Oz-113/deskie-vibed/source_frames/lucycigarette_7.png

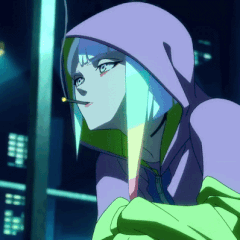
source_frames/lucycigarette_7.png
