Oz-113/deskie-vibed/source_frames/2b_0.png

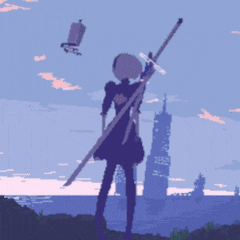
source_frames/2b_0.png
