Oz-113/deskie-vibed/source_frames/cirilla_0.png

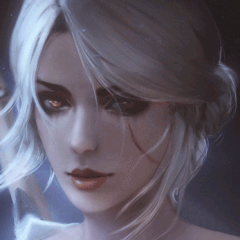
source_frames/cirilla_0.png
