Oz-113/deskie-vibed/source_frames/cirilla_11.png

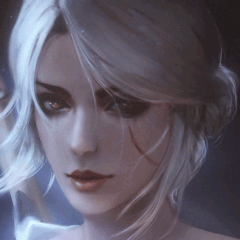
source_frames/cirilla_11.png
