Oz-113/deskie-vibed/source_frames/lucybg_0.png

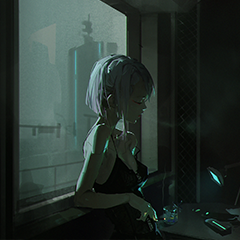
source_frames/lucybg_0.png
