Oz-113/deskie-vibed/source_frames/lucydavidmoon_0.png

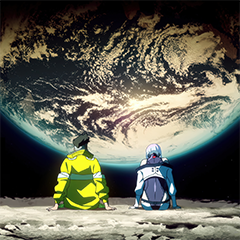
source_frames/lucydavidmoon_0.png
