Oz-113/deskie-vibed/CAD/hazir parcalar/esp32-s3-wroom-1-1.snapshot.2/WS2812B.SLDPRT

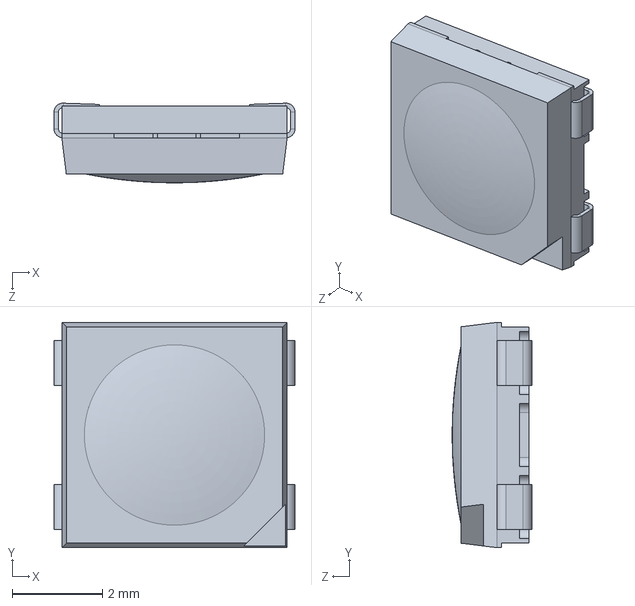
[picture p19: CAD file, 2026-09-12]
CAD/hazir parcalar/esp32-s3-wroom-1-1.snapshot.2/WS2812B.SLDPRT
5.35 x 5.00 x 1.77 mm
