Oz-113/deskie-vibed/CAD/hazir parcalar/esp32-s3-wroom-1-1.snapshot.2/SOT23-3.SLDPRT

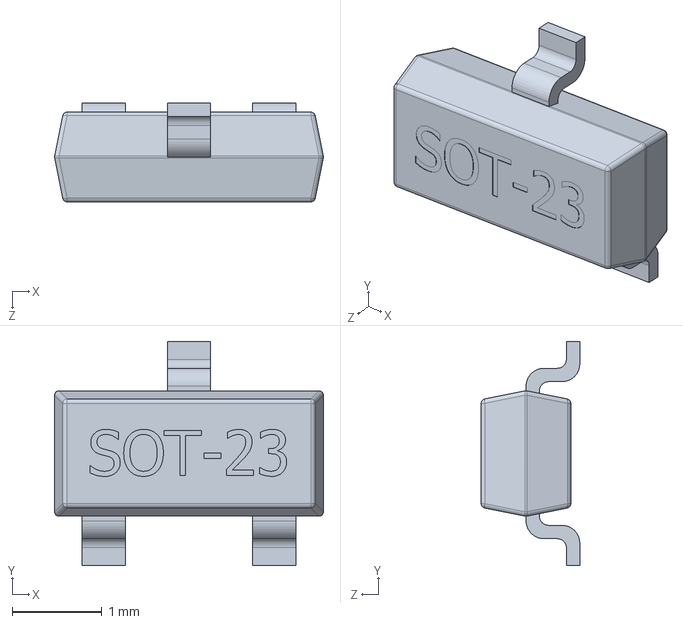
[picture p20: CAD file, 2026-09-12]
CAD/hazir parcalar/esp32-s3-wroom-1-1.snapshot.2/SOT23-3.SLDPRT
3.00 x 2.50 x 1.10 mm
