Oz-113/deskie-vibed/CAD/hazir parcalar/esp32-s3-wroom-1-1.snapshot.2/SOD-123F.SLDPRT

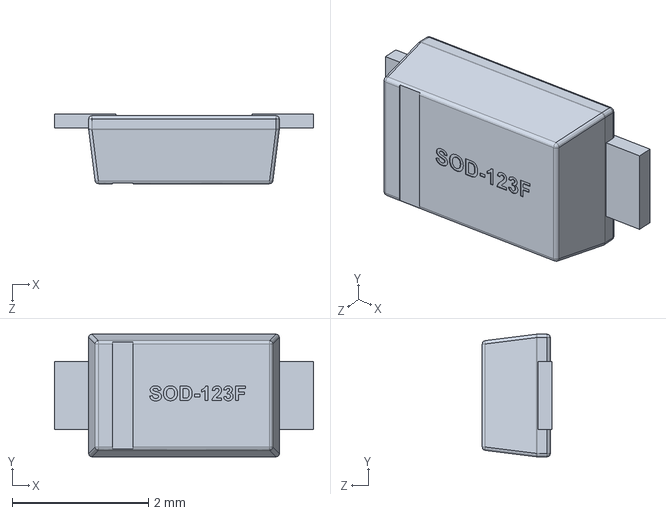
[picture p21: CAD file, 2026-09-12]
CAD/hazir parcalar/esp32-s3-wroom-1-1.snapshot.2/SOD-123F.SLDPRT
3.80 x 1.80 x 1.02 mm
