Oz-113/deskie-vibed/CAD/hazir parcalar/esp32-s3-wroom-1-1.snapshot.2/ctantal_case-a_l3-2_w1-6_h1-6.SLDPRT

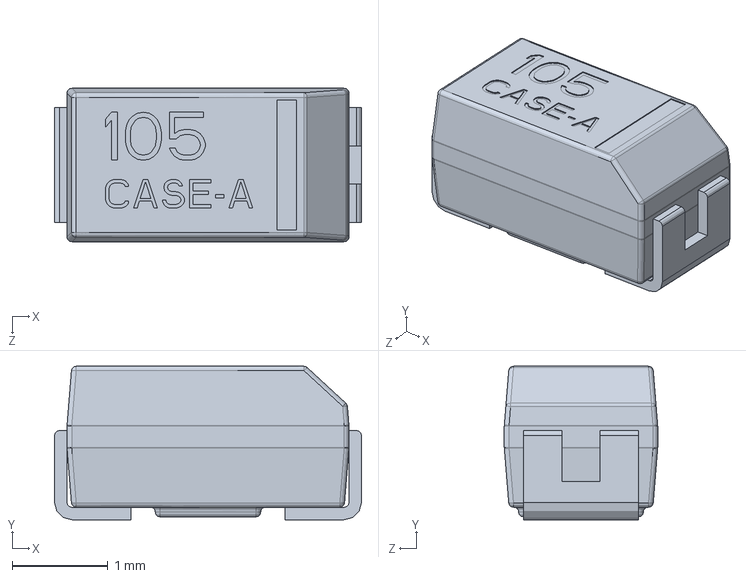
[picture p22: CAD file, 2026-09-12]
CAD/hazir parcalar/esp32-s3-wroom-1-1.snapshot.2/ctantal_case-a_l3-2_w1-6_h1-6.SLDPRT
3.20 x 1.60 x 1.60 mm
