Oz-113/deskie-vibed/CAD/hazir parcalar/esp32-s3-wroom-1-1.snapshot.2/RC0402.SLDPRT

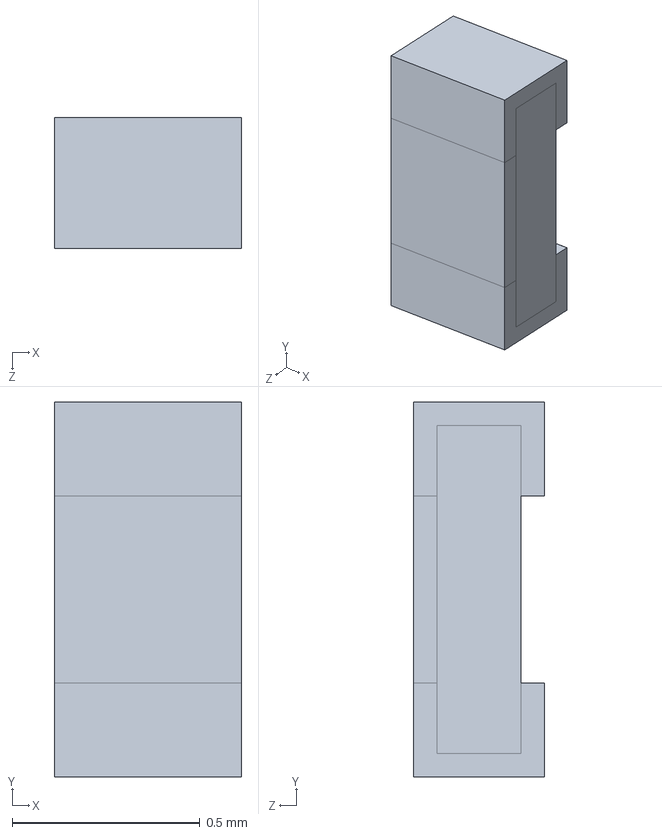
[picture p23: CAD file, 2026-09-12]
CAD/hazir parcalar/esp32-s3-wroom-1-1.snapshot.2/RC0402.SLDPRT
0.5 x 1.00 x 0.35 mm
