Oz-113/deskie-vibed/CAD/hazir parcalar/esp32-s3-wroom-1-1.snapshot.2/QFN-16 (3x3).SLDASM

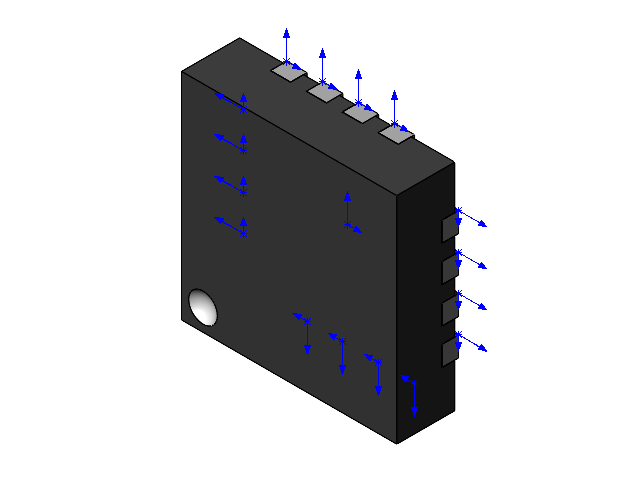
[picture p26: CAD file, 2026-09-12]
CAD/hazir parcalar/esp32-s3-wroom-1-1.snapshot.2/QFN-16 (3x3).SLDASM
QFN-16 (3x3) Part1.stp
QFN-16 (3x3) Part2.stp x 16
eBom-FreeParts.stp
