Oz-113/deskie-vibed/CAD/hazir parcalar/esp32-s3-wroom-1-1.snapshot.2/LED_0603 v4.SLDASM

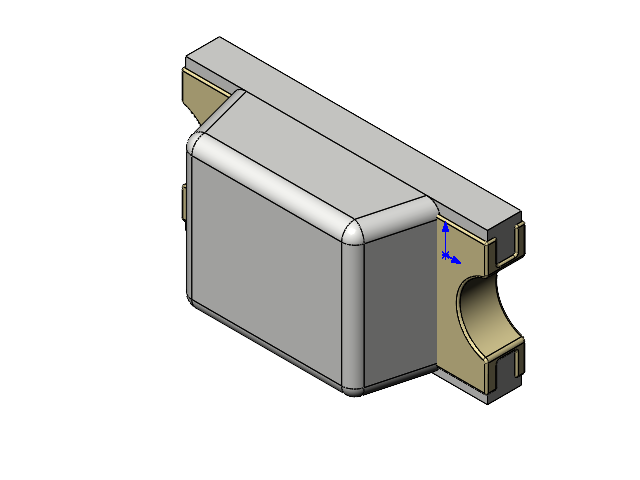
[picture p27: CAD file, 2026-09-12]
CAD/hazir parcalar/esp32-s3-wroom-1-1.snapshot.2/LED_0603 v4.SLDASM
Body.step
Cover.step
Cover_Mini.step
Insides.step
